OrangeFox86/DreamPicoPort/inc/hal/System/DppSettings.hpp

// MIT License
//
// Copyright (c) 2022-2026 The DreamPicoPort Contributors
// https://github.com/OrangeFox86/DreamcastControllerUsbPico
//
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
#pragma once

#include "configuration.h"

#include <cstdint>
#include <optional>
#include <functional>

struct DppSettings
{
    //! Number of players supported
    static const uint8_t kNumPlayers = 4;

    //! Enumerates the different player detection modes
    enum class PlayerDetectionMode : std::uint8_t
    {
        //! No auto detection, always disabled
        kDisable = 0,
        //! No auto detection, always enabled
        kEnable,
        //! Any value greater than this value is automatic detection
        kAutoThreshold = kEnable,
        //! Initially disabled, switch to kEnable and save settings once detected
        kAutoStatic,
        //! Any value greater than this value is automatic-dynamic detection
        kAutoDynamicThreshold = kAutoStatic,
        //! Auto detection, disabling and enabling as device is detected or removed
        kAutoDynamic,
        //! Auto detection, enabling as device is detected, only disabled upon power loss
        kAutoDynamicNoDisable,

        //! A count of number of modes
        kNumPlayerDetectionModes
    };

    //! Enumerates D-Pad output types
    enum class DpadType : std::uint8_t {
        kHat = 0,  //!< Output to hat switch
        kButtons,  //!< Output to discrete buttons
        kBoth,     //!< Output to both hat switch and discrete buttons

        kNumDpadTypes //!< A count of number of DpadTypes
    };

    //! USB CDC enabled flag (default: true)
    bool cdcEn = true;
    //! USB MSC enabled flag (default: false)
    bool mscEn = false;
    //! USB WebUSB announcement enabled flag (default: true)
    bool webUsbAnnounceEn = true;
    //! Detection mode for each player
    PlayerDetectionMode playerDetectionModes[kNumPlayers] = {
        PlayerDetectionMode::kAutoStatic,
        PlayerDetectionMode::kAutoStatic,
        PlayerDetectionMode::kAutoStatic,
        PlayerDetectionMode::kAutoStatic
    };
    //! GPIO number of maple A, maple B is always very next one
    int32_t gpioA[kNumPlayers] = {
        P1_BUS_START_PIN,
        P2_BUS_START_PIN,
        P3_BUS_START_PIN,
        P4_BUS_START_PIN
    };
    //! GPIO number of direction output (-1 to disable)
    int32_t gpioDir[kNumPlayers] = {
        P1_DIR_PIN,
        P2_DIR_PIN,
        P3_DIR_PIN,
        P4_DIR_PIN
    };
    //! true if output is high when currently outputting, false for opposite
    bool gpioDirOutputHigh[kNumPlayers] = {
        DIR_OUT_HIGH,
        DIR_OUT_HIGH,
        DIR_OUT_HIGH,
        DIR_OUT_HIGH
    };
    //! LED GPIO number for USB activity or -1 to disable
    //! When USB connected:
    //!   Default: ON
    //!   When controller key pressed: OFF
    //! When USB disconnected:
    //!   Default: OFF
    //!   When controller key pressed: Flashing quick
    int32_t usbLedGpio = USB_LED_PIN;
    //! LED GPIO number for simple USB activity or -1 to disable
    //! ON when USB connected; OFF when disconnected
    int32_t simpleUsbLedGpio = SIMPLE_USB_LED_PIN;
    //! The D-Pad output type
    DpadType dpadType = DpadType::kHat;

    //! Initializes and loads settings
    //! @pre must be called before interrupts or core 1 is started
    //! @return loaded settings
    static const DppSettings& initialize();

    //! @return the settings loaded on initialize()
    static const DppSettings& getInitialSettings();

    //! Called from core 1 to request save on core 0
    //! @param[in] delayMs Number of ms to delay before saving
    void requestSave(uint32_t delayMs);

    //! Called from core 1 to request settings clear on core 0
    //! @param[in] delayMs Number of ms to delay before saving
    static void requestClear(uint32_t delayMs);

    //! Processes any save requests
    //! @param[in] hwStopFn The function to call if the function is about to process a save
    static void processSaveRequests(const std::function<void()>& hwStopFn);

    //! Save settings to flash and reboots system
    //! @pre this must be called from core 0!
    //! @param[in] delayMs Number of milliseconds to delay before rebooting
    void save(uint32_t delayMs = 0) const;

    //! Forces valid settings
    //! @param[in] disablePlayerOnBadGpio Set to true to disable player if its gpio is invalid
    //! @return true iff settings were already valid
    bool makeValid(bool disablePlayerOnBadGpio = false);

    //! @pre DppSettings::initialize() must have been called
    //! @return the offset address in flash where settings are located
    static inline uint32_t getSettingsOffsetAddr()
    {
        return sSettingsOffsetAddr;
    }

    //! @return true iff the given gpio is valid
    static bool isGpioValid(std::int32_t gpio);

    //! @return true iff the given gpio is valid
    static bool isGpioValid(std::uint32_t gpio);

private:
    //! Attempt to read settings at the given address
    //! @param[in] flashAddrOffset The flash address offset to read
    //! @return std::nullopt if data at the given address is invalid
    //! @return the read settings otherwise
    static std::optional<DppSettings> readSettingsAtAddr(uint32_t flashAddrOffset);

public:
    //! The value set to watchdog scratch 0 when reboot caused due to settings update
    static const uint32_t WATCHDOG_SETTINGS_UPDATED_MAGIC = 0xFD706823;

private:
    //! Offset address of settings within flash
    static uint32_t sSettingsOffsetAddr;
    //! The loaded settings on initialize()
    static DppSettings sLoadedSettings;
    //! Set to true when save or clear is requested
    static bool sSaveOrClearRequested;
    //! The delay to wait when above is true
    static uint32_t sDelayMs;
    //! The 32-bit save requested time
    static uint32_t sSaveRequestTime;
    //! The settings used to save when above is true
    static std::optional<DppSettings> sSaveRequestedSettings;
    //! Set to true once saving, no further save requests may be made
    static bool sSaving;
};
