OrangeFox86/DreamPicoPort/src/hal/MapleBus/MapleBus.hpp

// MIT License
//
// Copyright (c) 2022-2026 The DreamPicoPort Contributors
// https://github.com/OrangeFox86/DreamcastControllerUsbPico
//
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
#pragma once

#include <memory>
#include <limits>
#include "hal/MapleBus/MapleBusInterface.hpp"
#include "pico/stdlib.h"
#include "hardware/structs/systick.h"
#include "hardware/dma.h"
#include "configuration.h"
#include "utils.h"
#include "maple_in.pio.h"
#include "maple_out.pio.h"
#include "hardware/pio.h"

//! Handles communication over Maple Bus.
//!
//! @warning this class is not "thread safe" - it should only be used by 1 core.
class MapleBus : public MapleBusInterface
{
    public:
        //! Maple Bus constructor
        //! @param[in] pinA  GPIO index for pin A. The very next GPIO will be designated as pin B.
        //! @param[in] dirPin  GPIO pin which selects direction (-1 to disable)
        //! @param[in] dirOutHigh  True if dirPin should be high on write; false for low on write
        MapleBus(uint32_t pinA, int32_t dirPin = -1, bool dirOutHigh = true);

        //! Writes a packet to the maple bus
        //! @post processEvents() must periodically be called to check status
        //! @param[in] packet  The packet to send (sender address will be overloaded)
        //! @param[in] autostartRead  Set to true in order to start receive after send is complete
        //! @param[in] readTimeoutUs  When autostartRead is true, the read timeout to set
        //! @param[in] rxBytePrder  When autostartRead is true, the desired byte order of the received packet
        //! @returns true iff the bus was "open" and send has started
        bool write(
            const MaplePacket& packet,
            bool autostartRead,
            uint32_t readTimeoutUs=MAPLE_RESPONSE_TIMEOUT_US,
            MaplePacket::ByteOrder rxByteOrder = MaplePacket::ByteOrder::HOST
        ) override;

        //! Begins waiting for input
        //! @post processEvents() must periodically be called to check status
        //! @note This is NOT meant to be called if bus is setup as a host
        //! @note Keep in mind that the maple_in state machine doesn't  sample the full end
        //!       sequence. The application side should wait a sufficient amount of time after bus
        //!       goes neutral before responding in that case. Waiting for neutral bus within
        //!       write() may be enough though (as long as MAPLE_OPEN_LINE_CHECK_TIME_US is set to
        //!       at least 2).
        //! @param[in] readTimeoutUs  Minimum number of microseconds to read for (optional)
        //! @param[in] rxByteOrder  The desired byte order of the received packet
        //! @returns true iff bus was not busy and read started
        bool startRead(
            uint32_t readTimeoutUs=NO_TIMEOUT,
            MaplePacket::ByteOrder rxByteOrder = MaplePacket::ByteOrder::HOST
        ) override;

        //! Called from a PIO ISR when read has completed for this sender.
        void readIsr();

        //! Called from a PIO ISR when write has completed for this sender.
        void writeIsr();

        //! Processes timing events for the current time. This should be called before any write
        //! call in order to check timeouts and clear out any used resources.
        //! @param[in] currentTimeUs  The current time to process for
        //! @returns updated status since last call
        Status processEvents(uint64_t currentTimeUs) override;

        //! @returns true iff the bus is currently busy reading or writing.
        inline bool isBusy() override { return mCurrentPhase != Phase::IDLE; }

        //! Set the callback that gets executed when read or write completes
        //! @note the callback may be called within ISR context, so it should be defined as __not_in_flash_func()
        //! @param[in] fn The function to call
        //! @param[in] context The context to pass to each function call
        void setCallback(void (*fn)(void*, uint32_t, Phase), void* context) override;

        //! @return the current statistics of this maple bus
        MapleStats getStats() const override;

    private:
        //! Ensures that the bus is open
        bool lineCheck();

        //! Set direction
        //! @param[in] output  True for output from this device or false for input to this device
        void setDirection(bool output);

        //! Reset all state machines
        void resetSms();

        //! Adds bytes to a CRC
        //! @param[in] source  Source array to read from
        //! @param[in] len  Number of words in source
        //! @param[in,out] crc  The crc to add to
        static void crc8(volatile const uint32_t *source, uint32_t len, uint8_t &crc);

        //! Adds bytes of a single word to a CRC
        //! @param[in] source  Source word to read from
        //! @param[in,out] crc  The crc to add to
        static void crc8(uint32_t source, uint8_t &crc);

        //! Copies words from source to dest
        //! @param[out] dest  The destination array to write to
        //! @param[in] source  The source array to read from
        //! @param[in] len  Number of words to copy
        static void wordCpy(
            volatile uint32_t* dest,
            volatile const uint32_t* source,
            uint32_t len
        );

        //! Flips the endianness of a word
        //! @param[in] word  Input word
        //! @returns output word
        static uint32_t flipWordBytes(const uint32_t& word);

        //! Initializes all interrupt service routines for all Maple Busses
        static void initIsrs();

    public:
        //! Timeout value to use when no timeout is desired
        static const uint32_t NO_TIMEOUT = std::numeric_limits<uint32_t>::max();

    private:
        //! Pin A GPIO index for this bus
        const uint32_t mPinA;
        //! Pin B GPIO index for this bus
        const uint32_t mPinB;
        //! Direction pin or -1 if not defined
        const int32_t mDirPin;
        //! True to set dir pin high on write and low on read; false for opposite
        const bool mDirOutHigh;
        //! Pin A GPIO mask for this bus
        const uint32_t mMaskA;
        //! Pin B GPIO mask for this bus
        const uint32_t mMaskB;
        //! GPIO mask for all bits used by this bus
        const uint32_t mMaskAB;
        //! The PIO state machine used for output by this bus
        MapleOutStateMachine mSmOut;
        //! The PIO state machine index used for input by this bus
        MapleInStateMachine mSmIn;
        //! The DMA channel used for writing by this bus
        const int mDmaWriteChannel;
        //! The DMA channel used for reading by this bus
        const int mDmaReadChannel;

        //! The output word buffer - 256 + 2 extra words for bit count and CRC
        volatile uint32_t mWriteBuffer[258];
        //! The input word buffer - 256 + 1 extra word for CRC + 1 for overflow
        volatile uint32_t mReadBuffer[258];
        //! Persistent storage for external use after processEvents call
        uint32_t mLastRead[256];
        //! Current phase of the state machine
        volatile Phase mCurrentPhase;
        //! True if read should be started immediately after write has completed
        bool mExpectingResponse;
        //! The read timeout to use when mExpectingResponse is true
        uint32_t mResponseTimeoutUs;
        //! The receive byte order of the last received packet
        MaplePacket::ByteOrder mRxByteOrder;
        //! The last time a process was started
        uint64_t mProcStartTime;
        //! Duration from mProcStartTime that timeout will occur (atomic value)
        volatile uint32_t mProcKillOffsetUs;
        //! The last duration since mProcStartTime which number of received words changed
        volatile uint32_t mLastReceivedWordOffsetUs;
        //! The last sampled read word transfer count
        uint32_t mLastReadTransferCount;

        //! Stores the subset of MapleStats always written outside of ISR
        struct NonVolatileMapleStats
        {
            //! Number of read attempts where no activity is seen on the line (i.e. nothing attached)
            std::uint64_t numNullReads = 0;
            //! Number of read attempts that received a CRC which was invalid
            std::uint64_t numReadFailCrc = 0;
            //! Number of read attempts that completed but didn't receive enough data
            std::uint64_t numReadFailIncomplete = 0;
            //! Number of read attempts that overflowed the input DMA
            std::uint64_t numReadFailOverflow = 0;
            //! Number of read attempts that started but timed out
            std::uint64_t numReadFailTimeout = 0;
            //! The last time point where read was successful
            std::uint64_t lastReadCompleteTime = 0;

            //! Total number of write attempts
            std::uint64_t numWrites;
            //! Number of write attempts that failed
            std::uint64_t numWriteFail;
            //! The last time point where write was attempted
            std::uint64_t lastWriteStartTime = 0;
        } mNVStats;

        //! Stores the subset of MapleStats potentially updated by the ISR
        struct VolatileMapleStats
        {
            //! Total number of read attempts
            volatile std::uint64_t numReads = 0;
            //! The last time point where read was attempted
            volatile std::uint64_t lastReadStartTime = 0;

            //! The last time point where write was successful
            volatile std::uint64_t lastWriteCompleteTime = 0;
        } mVStats;

        //! The callback function to execute on phase change
        void (* volatile mCallbackFn)(void*, uint32_t, Phase);
        //! Context to pass to each call of mCallbackFn
        void* volatile mCallbackFnContext;
};

std::shared_ptr<MapleBusInterface> create_maple_bus(uint32_t pinA, int32_t dirPin, bool dirOutHigh);
