OrangeFox86/DreamPicoPort/src/hostLib/webusb_parsers/FlycastWebUsbCommandHandler.cpp

// MIT License
//
// Copyright (c) 2022-2026 The DreamPicoPort Contributors
// https://github.com/OrangeFox86/DreamcastControllerUsbPico
//
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
#include "FlycastWebUsbCommandHandler.hpp"

#include "hal/MapleBus/MaplePacket.hpp"
#include "hal/System/LockGuard.hpp"
#include "hal/Usb/usb_interface.hpp"

#include <cstring>
#include <cinttypes>

const std::uint8_t FlycastWebUsbCommandHandler::kInterfaceVersion[2] = {1, 0};

FlycastWebUsbCommandHandler::FlycastWebUsbCommandHandler(
    SystemIdentification& identification,
    const std::shared_ptr<MapleWebUsbCommandHandler>& mapleWebUsbCommandHandler,
    const std::map<uint8_t, DreamcastNodeData>& dcNodes
) :
    mIdentification(identification),
    mMapleWebUsbCommandHandler(mapleWebUsbCommandHandler),
    mDcNodes(dcNodes)
{}

void FlycastWebUsbCommandHandler::process(
    const std::uint8_t* payload,
    std::uint16_t payloadLen,
    const std::function<
        void(std::uint8_t responseCmd, const std::list<std::pair<const void*, std::uint16_t>>& payloadList)
    >& responseFn
)
{
    const std::uint8_t* eol = payload + payloadLen;
    const std::uint8_t* iter = payload;

    if (iter >= eol)
    {
        responseFn(kResponseCmdInvalid, {});
        return;
    }

    switch(*iter)
    {
        // X- to reset all or one of {X-0, X-1, X-2, X-3} to reset a specific player
        case '-':
        {
            // Remove minus
            ++iter;
            int idx = -1;
            if (iter < eol)
            {
                idx = *iter;
            }

            // Reset screen data
            if (idx < 0)
            {
                // all
                std::uint8_t count = 0;
                for (std::pair<const uint8_t, DreamcastNodeData>& node : mDcNodes)
                {
                    ++count;
                    node.second.playerData->screenData->resetToDefault();
                }
                std::string s = std::to_string(count);
                responseFn(kResponseSuccess, {{&count, 1}});
            }
            else
            {
                std::map<uint8_t, DreamcastNodeData>::iterator nodeIter = mDcNodes.find(idx);
                if (nodeIter != mDcNodes.end())
                {
                    nodeIter->second.playerData->screenData->resetToDefault();
                    const std::uint8_t count = 1;
                    responseFn(kResponseSuccess, {{&count, 1}});
                }
                else
                {
                    responseFn(kResponseFailure, {});
                }
            }
        }
        return;

        // XP[0-4][0-4] to change displayed port character
        case 'P':
        {
            // Remove P
            ++iter;
            int idxin = -1;
            if (iter < eol)
            {
                idxin = *iter++;
            }
            int idxout = -1;
            if (iter < eol)
            {
                idxout = *iter++;
            }

            std::map<uint8_t, DreamcastNodeData>::iterator dcNodeIter = mDcNodes.end();
            if (
                idxin >= 0 &&
                (dcNodeIter = mDcNodes.find(idxin)) != mDcNodes.end() &&
                idxout >= 0 &&
                static_cast<std::size_t>(idxout) < ScreenData::NUM_DEFAULT_SCREENS
            )
            {
                dcNodeIter->second.playerData->screenData->setDataToADefault(idxout);
                responseFn(kResponseSuccess, {});
            }
            else
            {
                responseFn(kResponseFailure, {});
            }
        }
        return;

        // XS to return serial
        case 'S':
        {
            char buffer[mIdentification.getSerialSize() + 1] = {0};
            mIdentification.getSerial(buffer, sizeof(buffer) - 1);
            buffer[sizeof(buffer) - 1] = '\0';
            responseFn(kResponseSuccess, {{buffer, strlen(buffer) + 1}});
        }
        return;

        // X?0, X?1, X?2, or X?3 will return summary for the given node index
        case '?':
        {
            // Remove question mark
            ++iter;
            int idx = -1;
            if (iter < eol)
            {
                idx = *iter;
            }

            std::map<uint8_t, DreamcastNodeData>::iterator dcNodeIter = mDcNodes.end();
            if (idx >= 0 && (dcNodeIter = mDcNodes.find(idx)) != mDcNodes.end())
            {
                std::string response;
                response.reserve(64);

                std::list<std::list<std::array<uint32_t, 2>>> summary = dcNodeIter->second.mainNode->getSummary();
                bool first = true;
                for (const auto& i : summary)
                {
                    if (!first)
                    {
                        // Semicolon means start of next peripheral data
                        response.push_back(';');
                    }

                    for (const auto& j : i)
                    {
                        // Pipe means a 4-byte value will follow (first is function code)
                        response.push_back('|');
                        uint32_t out = MaplePacket::flipWordBytes(j[0]);
                        const char* const p8Out = reinterpret_cast<const char*>(&out);
                        response.append(p8Out, 4);

                        // Pipe means a 4-byte value will follow (second is function definitions word)
                        response.push_back('|');
                        out = MaplePacket::flipWordBytes(j[1]);
                        response.append(p8Out, 4);
                    }

                    first = false;
                }

                responseFn(kResponseSuccess, {{response.data(), response.size()}});
            }
            else
            {
                responseFn(kResponseFailure, {});
            }
        }
        return;

        // XV to return interface version
        case 'V':
        {
            responseFn(kResponseSuccess, {{kInterfaceVersion, sizeof(kInterfaceVersion)}});
        }
        return;

        // XR[0-3] to get controller report
        case 'R':
        {
            // Remove the R
            ++iter;
            if (iter >= eol)
            {
                responseFn(kResponseCmdInvalid, {});
                return;
            }
            std::vector<std::uint8_t> state = get_controller_state(*iter);
            if (state.empty())
            {
                responseFn(kResponseFailure, {});
                return;
            }
            responseFn(kResponseSuccess, {{state.data(), state.size()}});
        }
        return;

        // XG[0-3] to refresh gamepad state over HID
        case 'G':
        {
            // Remove the G
            ++iter;
            if (iter >= eol)
            {
                responseFn(kResponseCmdInvalid, {});
                return;
            }
            const std::uint8_t idx = *iter;
            std::map<uint8_t, DreamcastNodeData>::iterator dcNodeIter = mDcNodes.find(idx);
            if (dcNodeIter == mDcNodes.end())
            {
                responseFn(kResponseFailure, {});
                return;
            }
            dcNodeIter->second.playerData->gamepad.forceSend();
            responseFn(kResponseSuccess, {});
        }
        return;

        // XO to get connected gamepads
        case 'O':
        {
            // For each, 0 means unavailable, 1 means available but not connected, 2 means available and connected
            std::vector<std::uint8_t> connected(DppSettings::kNumPlayers, 0);
            for (std::pair<const uint8_t, DreamcastNodeData>& node : mDcNodes)
            {
                if (!node.second.playerDef->autoDetectOnly)
                {
                    connected[node.first] = node.second.mainNode->isDeviceDetected() ? 2 : 1;
                }
            }
            responseFn(kResponseSuccess, {{connected.data(), connected.size()}});
        }
        return;

        // Maple Bus passthrough
        case 0x05:
        {
            // Remove start character
            ++iter;
            std::uint16_t size = payloadLen - 1;

            // Process through the MapleWebUsbCommandHandler
            auto rv = mMapleWebUsbCommandHandler->processMaplePacket(iter, size, responseFn);

            if (!rv.first || !rv.second.isValid())
            {
                // Failed
                return;
            }

            // Check for special commands to process
            if (rv.second.command == 0x0C && rv.second.length == 0x32 && size >= 204)
            {
                uint32_t fn = 0;
                uint32_t loc = 0;
                memcpy(&fn, iter + 4, 4);
                memcpy(&loc, iter + 8, 4);
                fn = MaplePacket::flipWordBytes(fn);
                loc = MaplePacket::flipWordBytes(loc);
                if (fn == DEVICE_FN_LCD && loc == 0)
                {
                    // Save screen data
                    uint32_t screenWords[48];
                    memcpy(screenWords, iter + 12, 48 * sizeof(uint32_t));
                    for (uint32_t i = 0; i < 48; ++i)
                    {
                        screenWords[i] = MaplePacket::flipWordBytes(screenWords[i]);
                    }
                    rv.first->playerData->screenData->setData(screenWords, 0, 0x30, false);
                }
            }
        }
        return;

        default:
            responseFn(kResponseCmdInvalid, {{nullptr, 0}});
            return;
    }
}
