OrangeFox86/DreamPicoPort/src/hostLib/webusb_parsers/SettingsWebUsbCommandHandler.cpp

// MIT License
//
// Copyright (c) 2022-2026 The DreamPicoPort Contributors
// https://github.com/OrangeFox86/DreamcastControllerUsbPico
//
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
#include "SettingsWebUsbCommandHandler.hpp"

#include <cstring>

SettingsWebUsbCommandHandler::SettingsWebUsbCommandHandler() :
    mLoadedSettings(DppSettings::getInitialSettings()),
    mSettings(mLoadedSettings)
{}

static std::uint32_t flip_word_bytes(const int32_t& word)
{
    const std::uint32_t wordU32 = static_cast<std::uint32_t>(word);
    return (wordU32 << 24) | (wordU32 << 8 & 0xFF0000) | (wordU32 >> 8 & 0xFF00) | (wordU32 >> 24);
}

static std::string packSettings(const DppSettings& settings)
{
    std::string settingsData;

    settingsData.reserve(52);
    settingsData.push_back(static_cast<std::uint8_t>(settings.cdcEn ? 1 : 0));
    settingsData.push_back(static_cast<std::uint8_t>(settings.mscEn ? 1 : 0));
    settingsData.push_back(static_cast<std::uint8_t>(settings.webUsbAnnounceEn ? 1 : 0));

    for (std::uint8_t i = 0; i < DppSettings::kNumPlayers; ++i)
    {
        settingsData.push_back(static_cast<std::uint8_t>(settings.playerDetectionModes[i]));
    }

    for (std::uint8_t i = 0; i < DppSettings::kNumPlayers; ++i)
    {
        std::uint32_t val = flip_word_bytes(settings.gpioA[i]);
        settingsData.append(reinterpret_cast<const char*>(&val), sizeof(val));
    }

    for (std::uint8_t i = 0; i < DppSettings::kNumPlayers; ++i)
    {
        std::int32_t val = flip_word_bytes(settings.gpioDir[i]);
        settingsData.append(reinterpret_cast<const char*>(&val), sizeof(val));
    }

    for (std::uint8_t i = 0; i < DppSettings::kNumPlayers; ++i)
    {
        settingsData.push_back(static_cast<std::uint8_t>(settings.gpioDirOutputHigh[i]));
    }

    std::int32_t v = flip_word_bytes(settings.usbLedGpio);
    settingsData.append(reinterpret_cast<const char*>(&v), sizeof(v));

    v = flip_word_bytes(settings.simpleUsbLedGpio);
    settingsData.append(reinterpret_cast<const char*>(&v), sizeof(v));

    settingsData.push_back(static_cast<std::uint8_t>(settings.dpadType));

    return settingsData;
}

void SettingsWebUsbCommandHandler::process(
    const std::uint8_t* payload,
    std::uint16_t payloadLen,
    const std::function<
        void(std::uint8_t responseCmd, const std::list<std::pair<const void*, std::uint16_t>>& payloadList)
    >& responseFn
)
{
    const std::uint8_t* eol = payload + payloadLen;
    const std::uint8_t* iter = payload;

    if (iter >= eol)
    {
        responseFn(kResponseCmdInvalid, {});
        return;
    }

    const char cmd = *iter++;
    const std::size_t numPayload = (eol - iter);
    switch(cmd)
    {
        // Get all loaded settings
        case 'G':
        {
            std::string settingsData = packSettings(mLoadedSettings);
            responseFn(kResponseSuccess, {{settingsData.data(), settingsData.size()}});
        }
        return;

        // Get all locally-stored settings
        case 'g':
        {
            std::string settingsData = packSettings(mSettings);
            responseFn(kResponseSuccess, {{settingsData.data(), settingsData.size()}});
        }
        return;

        // Set USB CDC enabled flag
        case 'C':
        {
            if (numPayload < 1)
            {
                std::uint8_t payload = 0;
                responseFn(kResponseFailure, {{&payload, 1}});
                return;
            }

            mSettings.cdcEn = (*iter != 0);
            responseFn(kResponseSuccess, {});
        }
        return;

        // Set USB MSC enabled flag
        case 'M':
        {
            if (numPayload < 1)
            {
                std::uint8_t payload = 0;
                responseFn(kResponseFailure, {{&payload, 1}});
                return;
            }

            mSettings.mscEn = (*iter != 0);
            responseFn(kResponseSuccess, {});
        }
        return;

        // Set WebUSB announcement flag
        case 'W':
        {
            if (numPayload < 1)
            {
                std::uint8_t payload = 0;
                responseFn(kResponseFailure, {{&payload, 1}});
                return;
            }

            mSettings.webUsbAnnounceEn = (*iter != 0);
            responseFn(kResponseSuccess, {});
        }
        return;

        // Player detection mode: P[0-3][PlayerDetectionMode (1 byte)]
        case 'P':
        {
            if (numPayload < 2)
            {
                std::uint8_t payload = 0;
                responseFn(kResponseFailure, {{&payload, 1}});
                return;
            }

            std::uint8_t playerIdx = (*iter);
            if (playerIdx >= DppSettings::kNumPlayers)
            {
                std::uint8_t payload = 1;
                responseFn(kResponseFailure, {{&payload, 1}});
                return;
            }

            std::uint8_t playerDetectionMode = (*(iter + 1));
            if (
                playerDetectionMode >=
                static_cast<std::uint8_t>(DppSettings::PlayerDetectionMode::kNumPlayerDetectionModes)
            )
            {
                std::uint8_t payload = 2;
                responseFn(kResponseFailure, {{&payload, 1}});
                return;
            }

            mSettings.playerDetectionModes[playerIdx] =
                static_cast<DppSettings::PlayerDetectionMode>(playerDetectionMode);
            responseFn(kResponseSuccess, {});
        }
        return;

        // Player I/O settings: I[0-3][GPIO A (4 byte)][GPIO DIR (4 byte)][DIR Output HIGH (1 byte)]
        case 'I':
        {
            if (numPayload < 10)
            {
                std::uint8_t payload = 0;
                responseFn(kResponseFailure, {{&payload, 1}});
                return;
            }

            std::uint8_t playerIdx = (*iter);
            if (playerIdx >= DppSettings::kNumPlayers)
            {
                std::uint8_t payload = 1;
                responseFn(kResponseFailure, {{&payload, 1}});
                return;
            }

            std::int32_t gpioA;
            memcpy(&gpioA, iter + 1, 4);
            gpioA = flip_word_bytes(gpioA);
            if (!DppSettings::isGpioValid(gpioA))
            {
                std::uint8_t payload = 2;
                responseFn(kResponseFailure, {{&payload, 1}});
                return;
            }

            std::int32_t gpioDir;
            memcpy(&gpioDir, iter + 5, 4);
            gpioDir = flip_word_bytes(gpioDir);
            if (!DppSettings::isGpioValid(gpioDir))
            {
                std::uint8_t payload = 3;
                responseFn(kResponseFailure, {{&payload, 1}});
                return;
            }

            bool dirOutputHigh = ((*(iter + 9)) != 0);

            mSettings.gpioA[playerIdx] = gpioA;
            mSettings.gpioDir[playerIdx] = gpioDir;
            mSettings.gpioDirOutputHigh[playerIdx] = dirOutputHigh;
            responseFn(kResponseSuccess, {});
        }
        return;

        // LED setting L[LED Pin (4 byte)]
        case 'L':
        {
            if (numPayload < 4)
            {
                std::uint8_t payload = 0;
                responseFn(kResponseFailure, {{&payload, 1}});
                return;
            }

            std::int32_t usbLedGpio;
            memcpy(&usbLedGpio, iter, 4);
            usbLedGpio = flip_word_bytes(usbLedGpio);
            if (!DppSettings::isGpioValid(usbLedGpio))
            {
                std::uint8_t payload = 1;
                responseFn(kResponseFailure, {{&payload, 1}});
                return;
            }

            mSettings.usbLedGpio = usbLedGpio;
            responseFn(kResponseSuccess, {});
        }
        return;

        // Simple LED setting l[LED Pin (4 byte)]
        case 'l':
        {
            if (numPayload < 4)
            {
                std::uint8_t payload = 0;
                responseFn(kResponseFailure, {{&payload, 1}});
                return;
            }

            std::int32_t simpleUsbLedGpio;
            memcpy(&simpleUsbLedGpio, iter, 4);
            simpleUsbLedGpio = flip_word_bytes(simpleUsbLedGpio);
            if (!DppSettings::isGpioValid(simpleUsbLedGpio))
            {
                std::uint8_t payload = 1;
                responseFn(kResponseFailure, {{&payload, 1}});
                return;
            }

            mSettings.simpleUsbLedGpio = simpleUsbLedGpio;
            responseFn(kResponseSuccess, {});
        }
        return;

        // Set DPad output d[setting (1 byte)]
        case 'd':
        {
            if (numPayload < 1)
            {
                std::uint8_t payload = 0;
                responseFn(kResponseFailure, {{&payload, 1}});
                return;
            }
            else if (*iter >= static_cast<std::uint8_t>(DppSettings::DpadType::kNumDpadTypes))
            {
                std::uint8_t payload = 1;
                responseFn(kResponseFailure, {{&payload, 1}});
                return;
            }

            mSettings.dpadType = static_cast<DppSettings::DpadType>(*iter);
            responseFn(kResponseSuccess, {});
        }
        return;

        // Validate settings
        case 's':
        {
            uint8_t responseCmd = mSettings.makeValid() ? kResponseSuccess : kResponseAttention;
            std::string settingsData = packSettings(mSettings);
            responseFn(responseCmd, {{settingsData.data(), settingsData.size()}});
        }
        return;

        // Save all settings and reboot
        case 'S':
        {
            if (mSettings.makeValid())
            {
                responseFn(kResponseSuccess, {});
            }
            else
            {
                // Settings had to be adjusted to be valid, save and respond with adjusted settings
                std::string settingsData = packSettings(mSettings);
                responseFn(kResponseSuccess, {{settingsData.data(), settingsData.size()}});
            }

            // This will save and reboot on core 0 - delay for 100 ms to allow the above message to go out
            mSettings.requestSave(100);
        }
        return;

        // Get the defaults without resetting
        case 'x':
        {
            std::string settingsData = packSettings(DppSettings());
            responseFn(kResponseSuccess, {{settingsData.data(), settingsData.size()}});
        }
        return;

        // Clear all settings and reboot
        case 'X':
        {
            // Send the response with default settings
            std::string settingsData = packSettings(DppSettings());
            responseFn(kResponseSuccess, {{settingsData.data(), settingsData.size()}});

            // Clear in 100 ms
            DppSettings::requestClear(100);
        }
        return;

        // Invalid
        default:
            responseFn(kResponseCmdInvalid, {});
            return;
    }
}
